milogert/paint_case/case/6mm-case-test_cuts.dxf

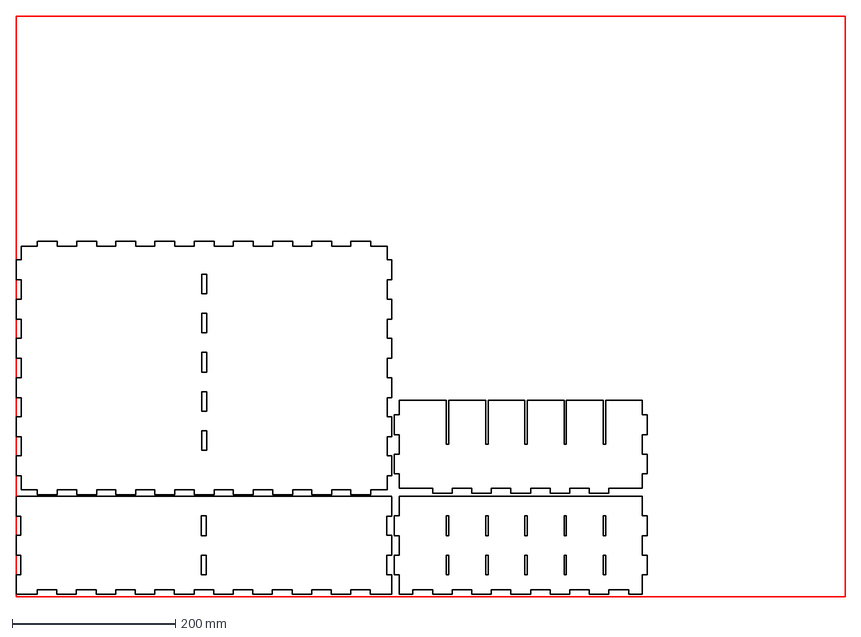
[picture p19: CAD file, 2021-03-29]
case/6mm-case-test_cuts.dxf
1015.0 x 711.0 mm
