milogert/paint_case/4.669mm/Drawer.dxf

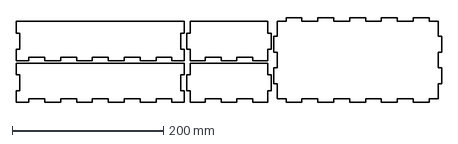
[picture p20: CAD file, 2021-02-04]
4.669mm/Drawer.dxf
562.0 x 112.0 mm
